Angjelo27/Noah/3d-models/STL/NOAH_FitCoupon_Magnet.stl

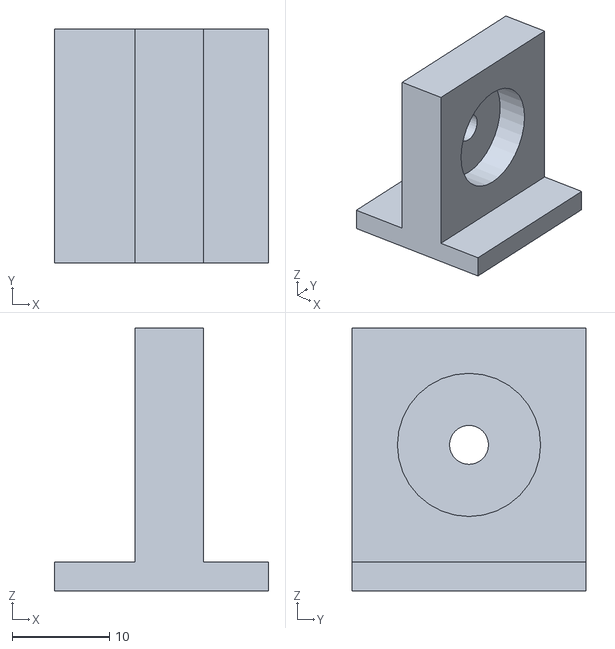
[picture p15: CAD file, 2026-09-03]
3d-models/STL/NOAH_FitCoupon_Magnet.stl
22.0 x 24.0 x 27.0
