Angjelo27/Noah/3d-models/Shell_Cuts/NOAH_ShellQ_Right_Bottom.stl

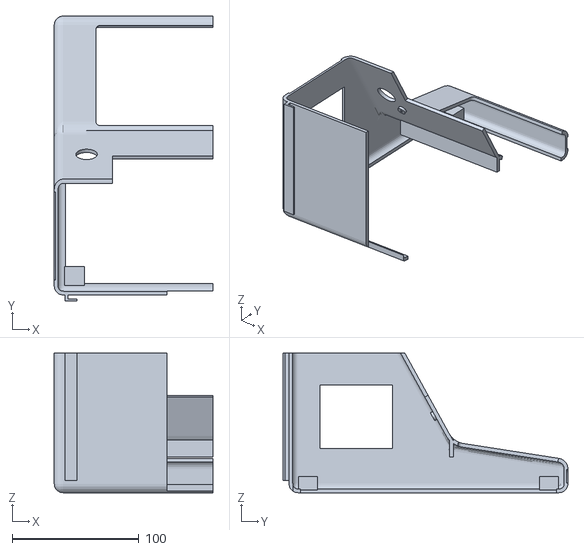
[picture p16: CAD file, 2026-09-03]
3d-models/Shell_Cuts/NOAH_ShellQ_Right_Bottom.stl
125.0 x 224.7 x 110.0
