Angjelo27/Noah/3d-models/STL/NOAH_SolarTabLock_L.stl

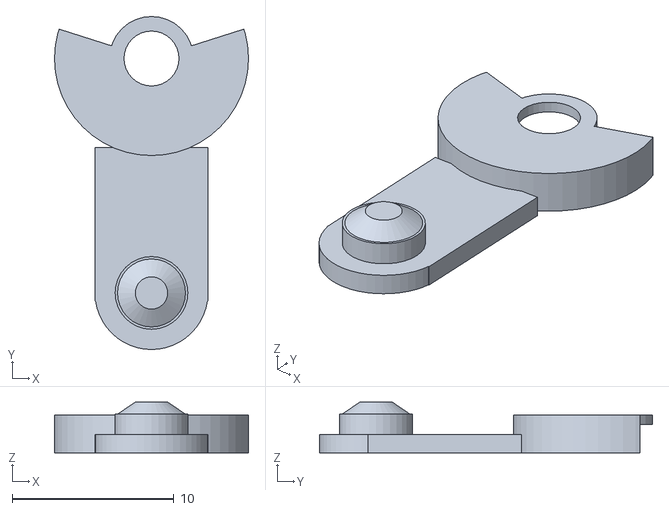
[picture p17: CAD file, 2026-09-03]
3d-models/STL/NOAH_SolarTabLock_L.stl
12.0 x 20.6 x 3.15
