Angjelo27/Noah/3d-models/Shell_Cuts/NOAH_ShellH_Top.stl

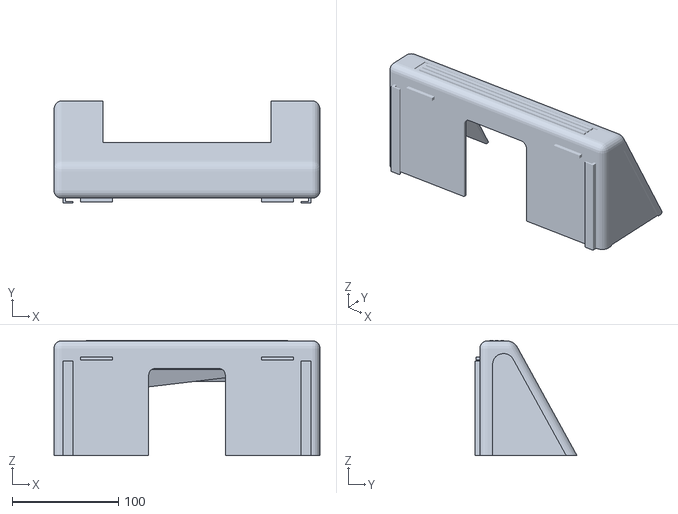
[picture p18: CAD file, 2026-09-03]
3d-models/Shell_Cuts/NOAH_ShellH_Top.stl
250.0 x 96.2 x 108.5
