Angjelo27/Noah/3d-models/STL/NOAH_Visor.stl

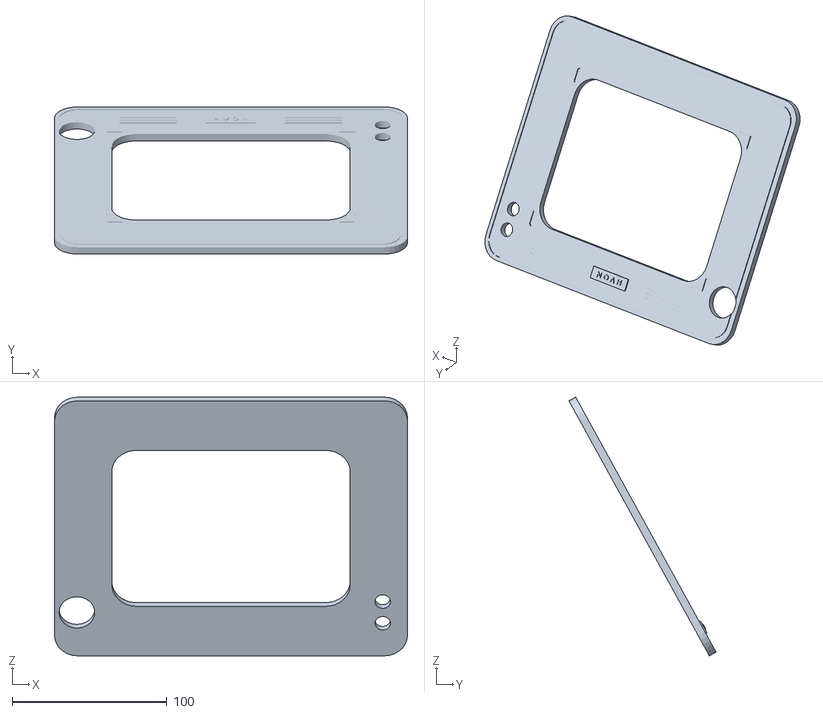
[picture p19: CAD file, 2026-09-03]
3d-models/STL/NOAH_Visor.stl
228.0 x 95.1 x 167.1
