Angjelo27/Noah/3d-models/STL/NOAH_Shell.stl

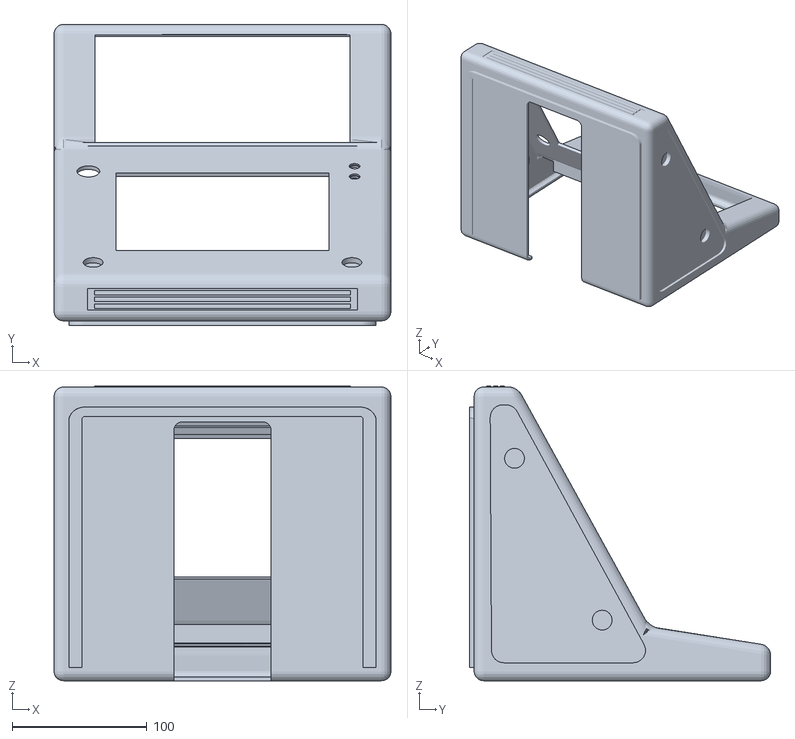
[picture p20: CAD file, 2026-09-03]
3d-models/STL/NOAH_Shell.stl
250.0 x 223.5 x 218.5
