Angjelo27/Noah/3d-models/STL/NOAH_FitCoupon_Rails.stl

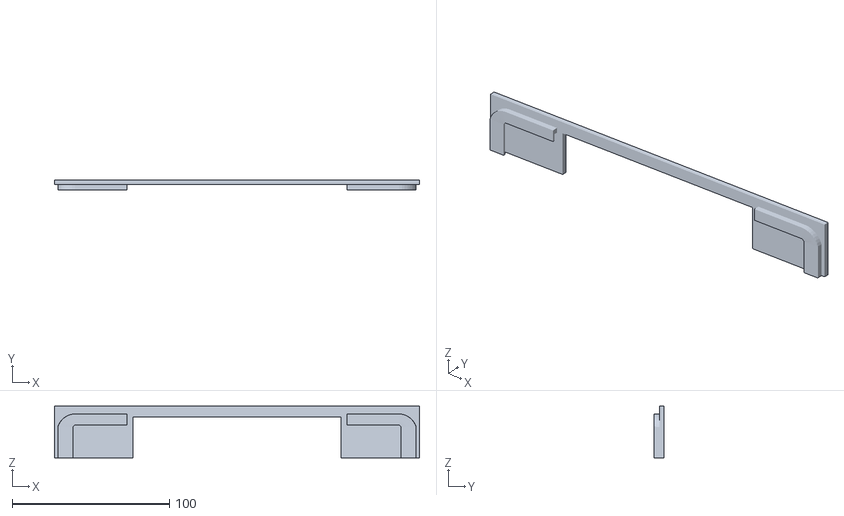
[picture p21: CAD file, 2026-09-03]
3d-models/STL/NOAH_FitCoupon_Rails.stl
232.0 x 6.50 x 33.0
