Angjelo27/Noah/3d-models/STL/NOAH_RubberBumpers.stl

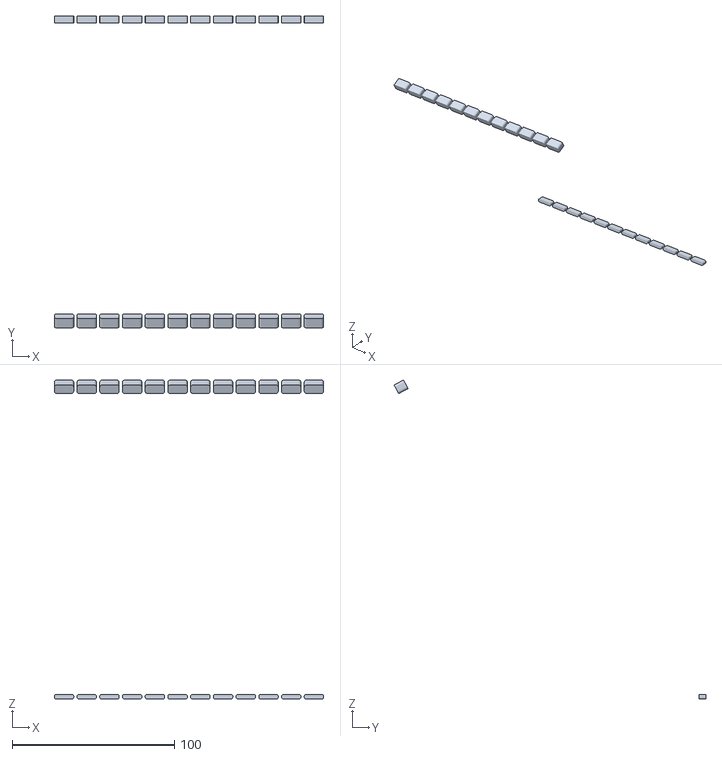
[picture p22: CAD file, 2026-09-03]
3d-models/STL/NOAH_RubberBumpers.stl
166.0 x 192.1 x 196.6
