Angjelo27/Noah/3d-models/STL/NOAH_RuggedTrim.stl

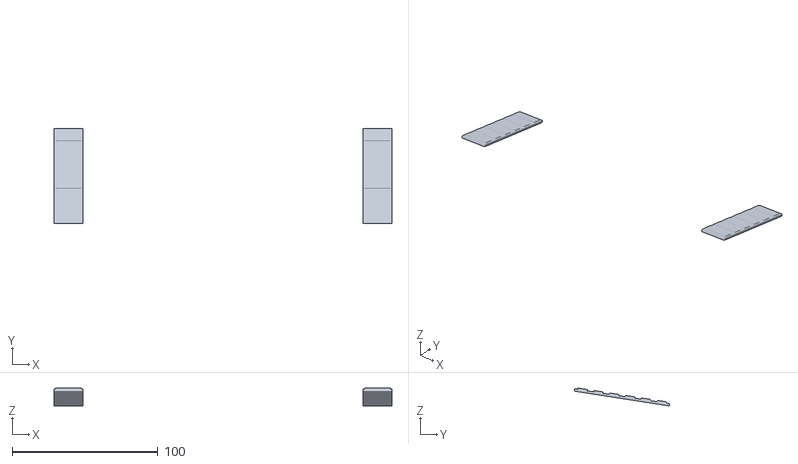
[picture p23: CAD file, 2026-09-03]
3d-models/STL/NOAH_RuggedTrim.stl
232.0 x 65.5 x 12.3
