Angjelo27/Noah/3d-models/STL/NOAH_BasePlate.stl

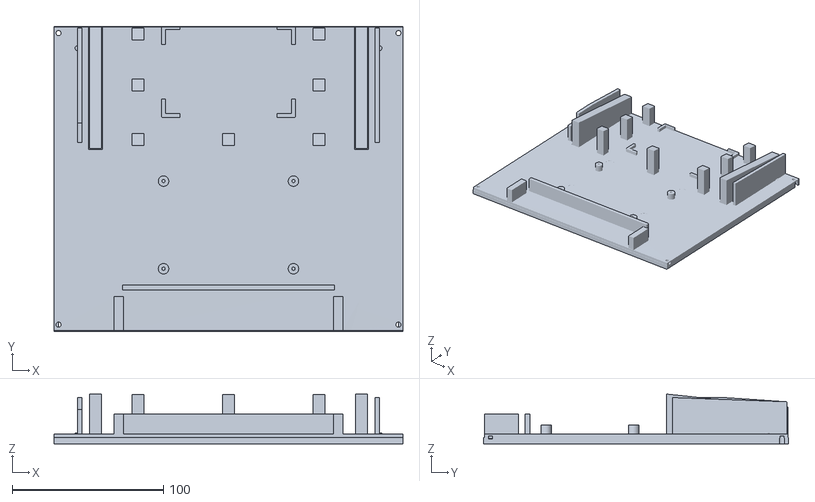
[picture p24: CAD file, 2026-09-03]
3d-models/STL/NOAH_BasePlate.stl
231.0 x 201.6 x 33.0
