Angjelo27/Noah/3d-models/STL/NOAH_SidePlate_R.stl

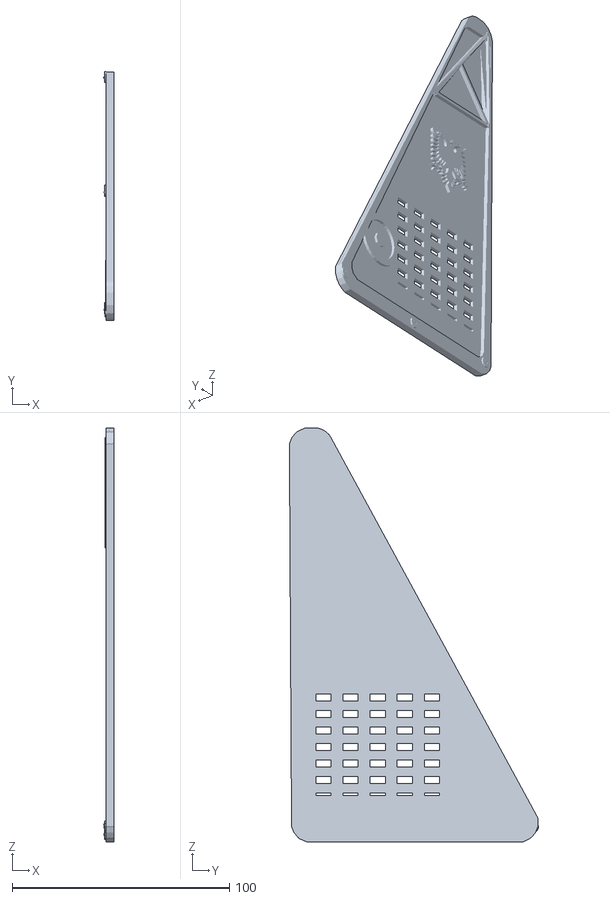
[picture p25: CAD file, 2026-09-03]
3d-models/STL/NOAH_SidePlate_R.stl
4.75 x 114.8 x 190.7
