Angjelo27/Noah/3d-models/STL/NOAH_LED_Lens.stl

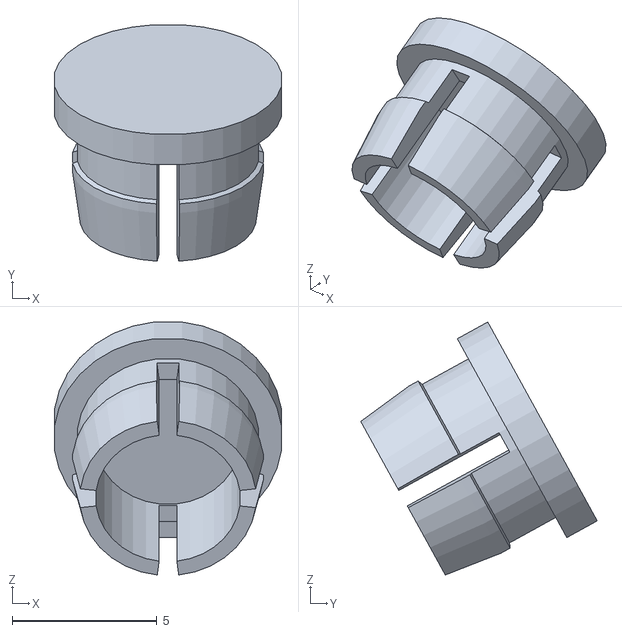
[picture p26: CAD file, 2026-09-03]
3d-models/STL/NOAH_LED_Lens.stl
7.84 x 8.17 x 8.74
